denisw160/CoffeeMonitor/documentation/CoffeeMonitor_MongoDB.png

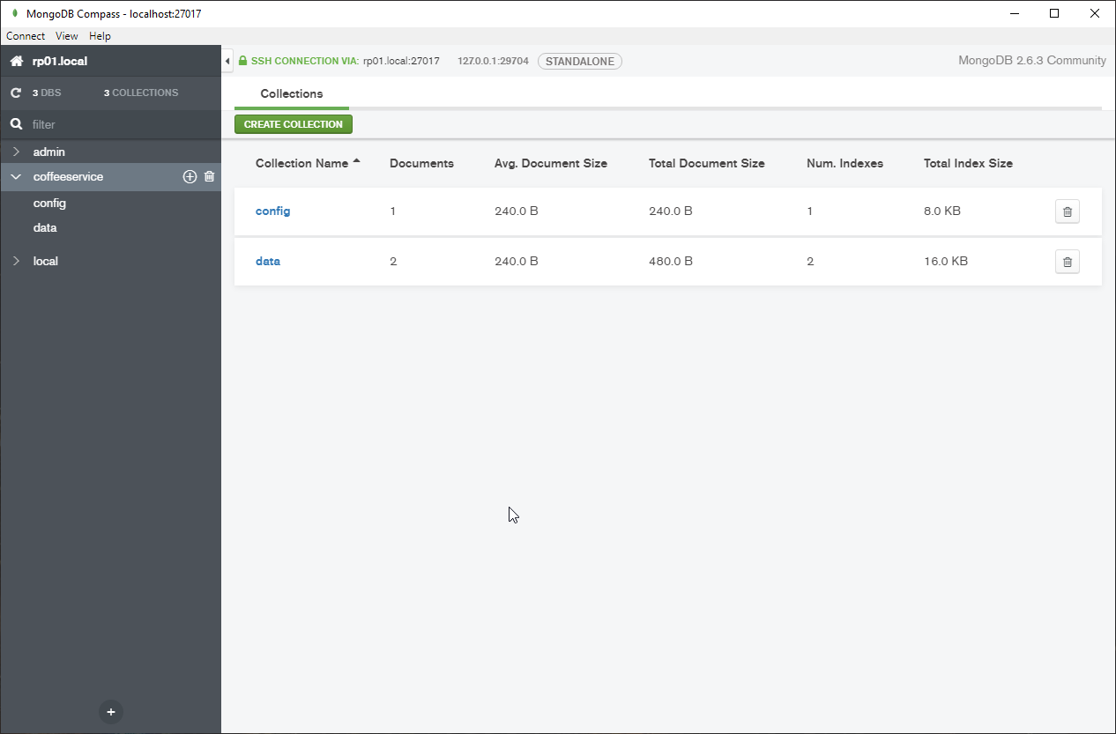
documentation/CoffeeMonitor_MongoDB.png
