denisw160/CoffeeMonitor/documentation/CoffeeMonitor_History2.png

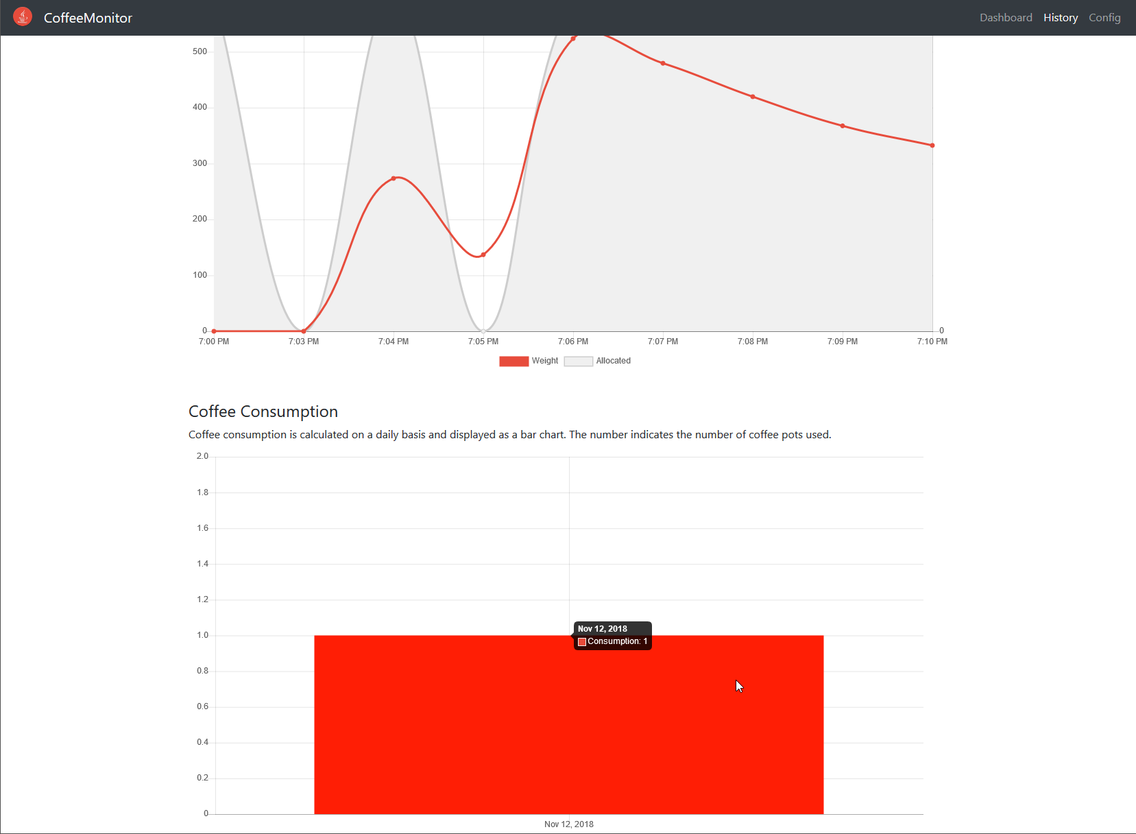
documentation/CoffeeMonitor_History2.png
